RadiationPAR/interfazProcessingRGBW/Diagramas/GENERAL.png

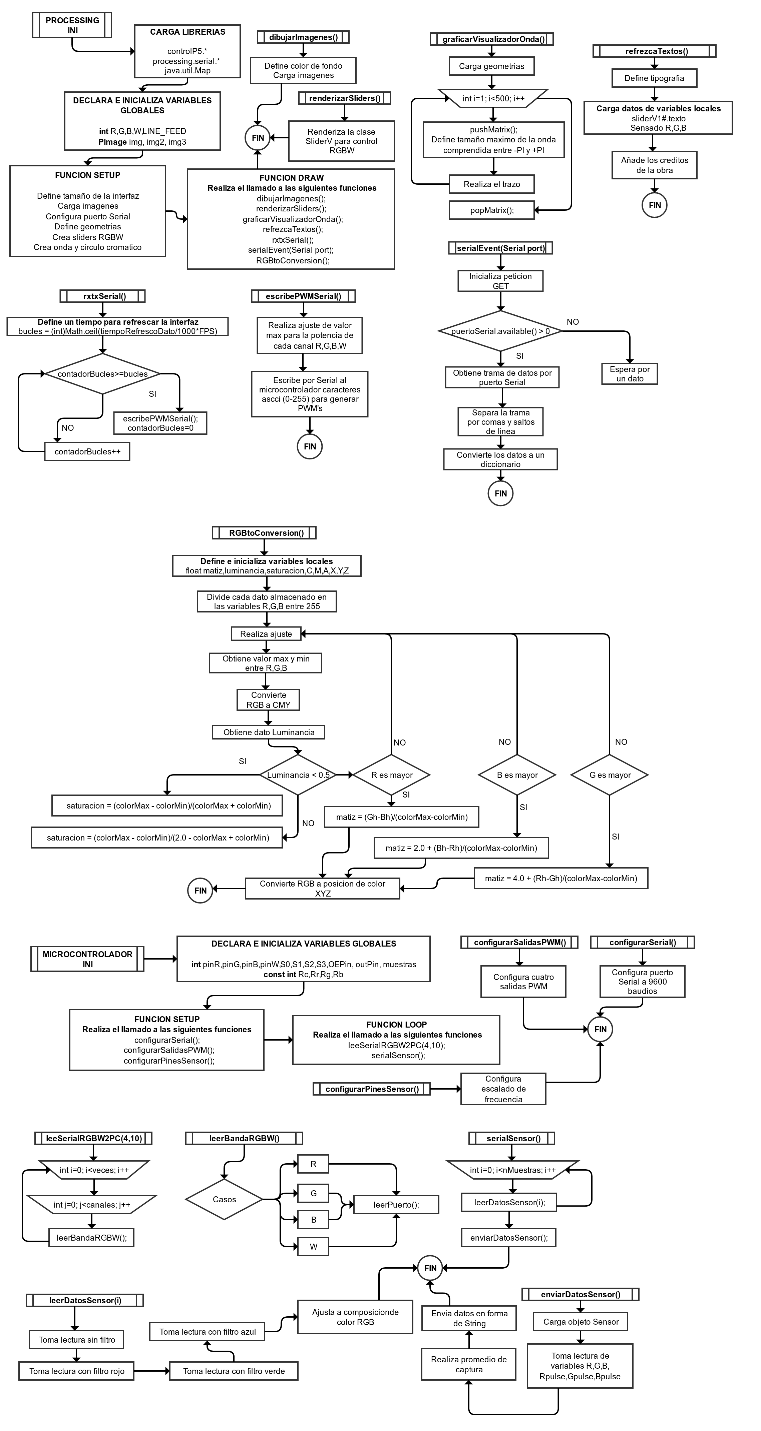
Diagramas/GENERAL.png
