RadiationPAR/interfazProcessingRGBW/Diagramas/PROCESSING1.png

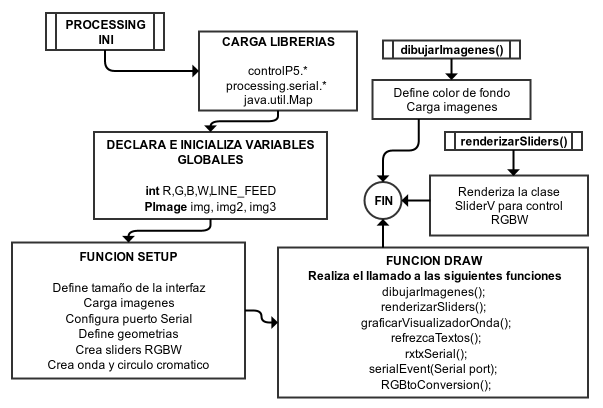
Diagramas/PROCESSING1.png
