RadiationPAR/interfazProcessingRGBW/Diagramas/PROCESSING2.png

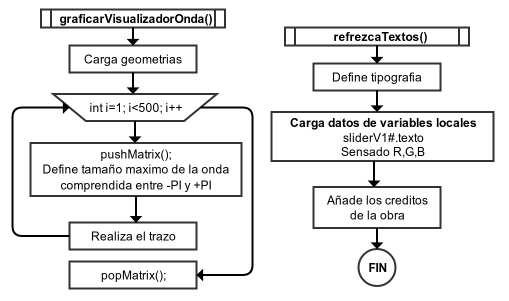
Diagramas/PROCESSING2.png
