RadiationPAR/interfazProcessingRGBW/Diagramas/PROCESSING3.png

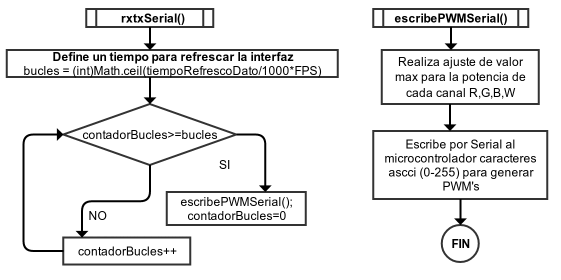
Diagramas/PROCESSING3.png
