RadiationPAR/interfazProcessingRGBW/Diagramas/PROCESSING4.png

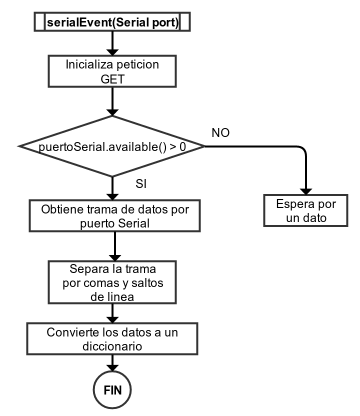
Diagramas/PROCESSING4.png
