RadiationPAR/interfazProcessingRGBW/Diagramas/PROCESSING.png

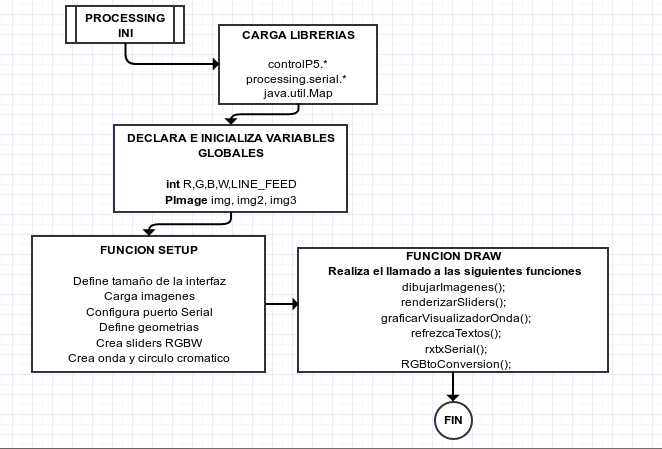
Diagramas/PROCESSING.png
