RadiationPAR/interfazProcessingRGBW/Diagramas/TIVA1.png

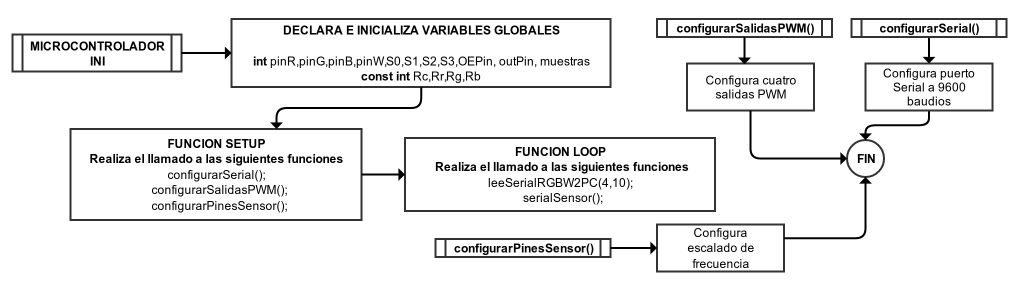
Diagramas/TIVA1.png
