RadiationPAR/interfazProcessingRGBW/Diagramas/TIVA2.png

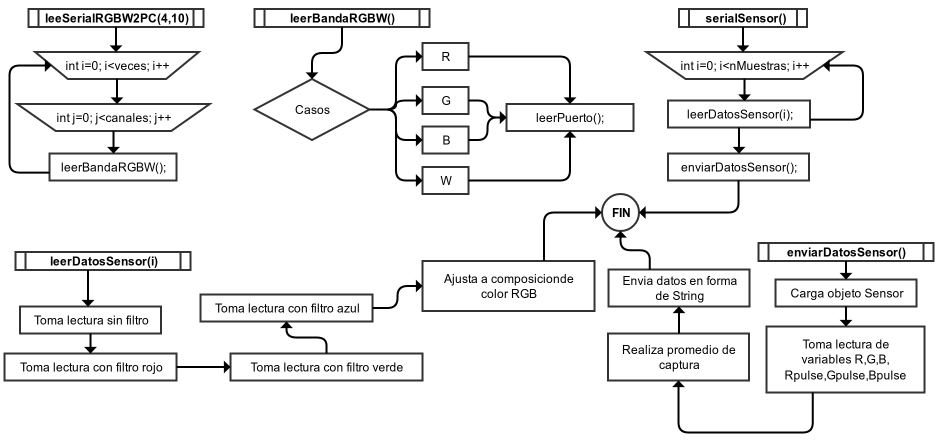
Diagramas/TIVA2.png
