RadiationPAR/interfazProcessingRGBW/interfaz/ProcessingControlRGBW/imagenes/cromatico.png

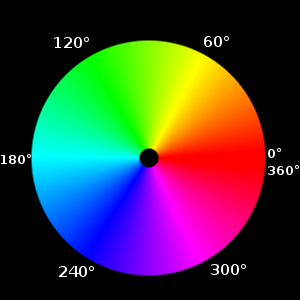
interfaz/ProcessingControlRGBW/imagenes/cromatico.png
