RadiationPAR/interfazProcessingRGBW/pruebasInstrumentacion/blue-471nm/medición 5.png

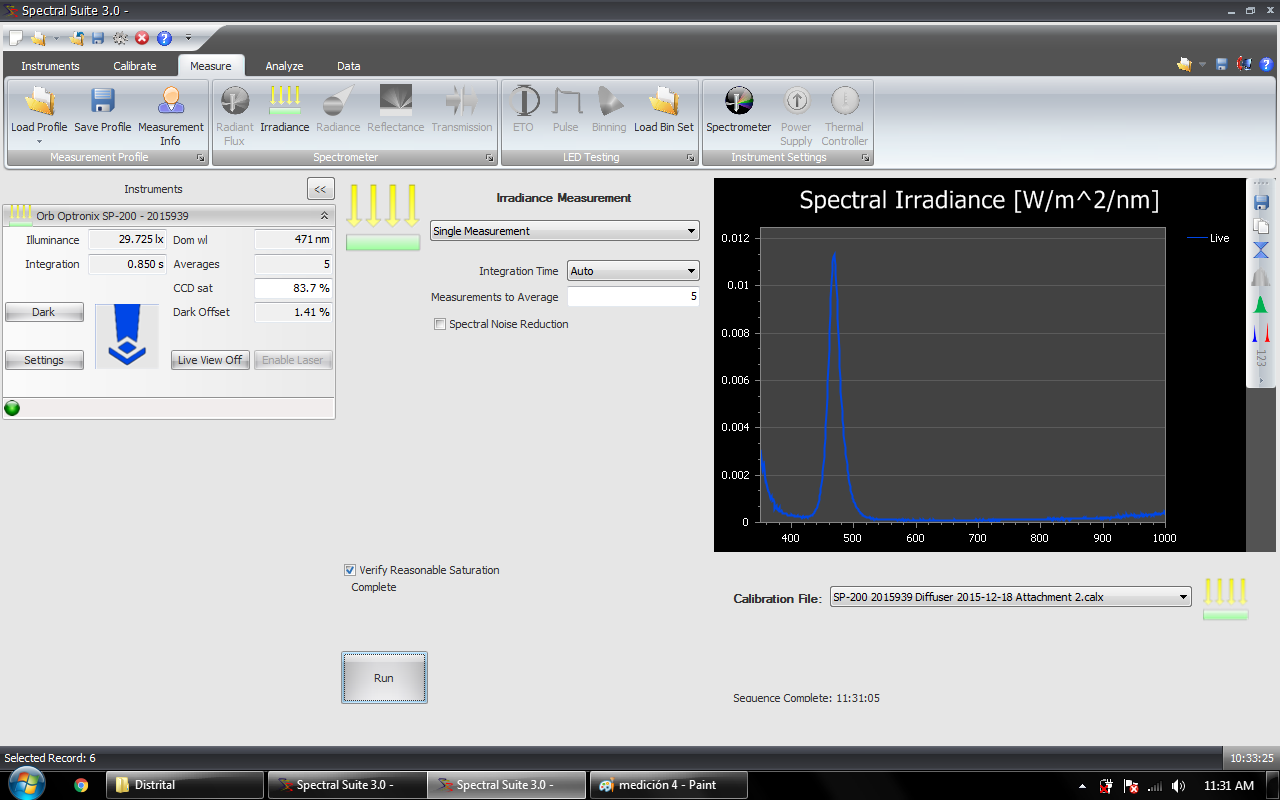
pruebasInstrumentacion/blue-471nm/medición 5.png
